techyg/VzBot/Config/inputshaper.cfg

[mcu ampon]
serial: /dev/serial/by-id/usb-Anchor_Ampon-if00

[adxl345]
cs_pin: ampon:CS

[resonance_tester]
accel_chip: adxl345
probe_points: 150, 150, 25
